tolgaozuygur/nightvision/pictures/20230412_170507.jpg

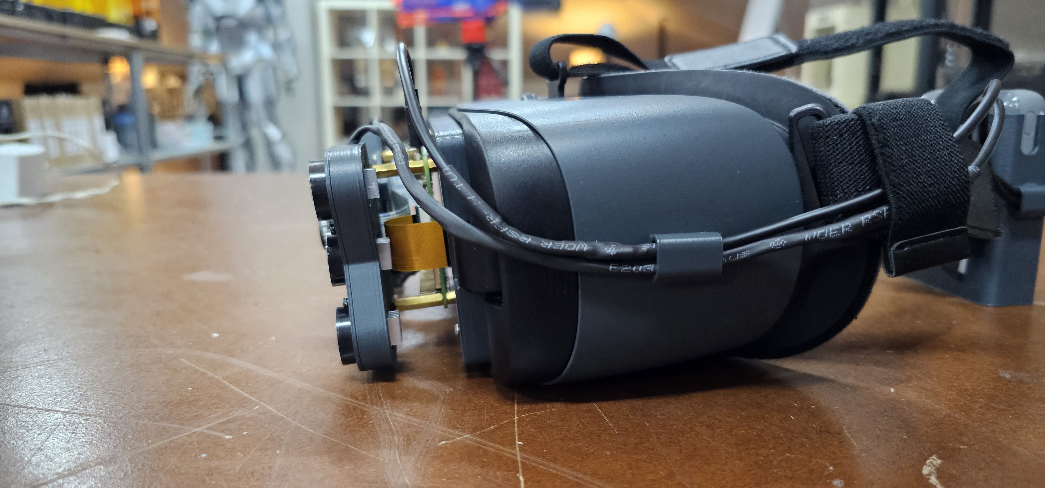
pictures/20230412_170507.jpg
