tolgaozuygur/nightvision/pictures/20230412_170524.jpg

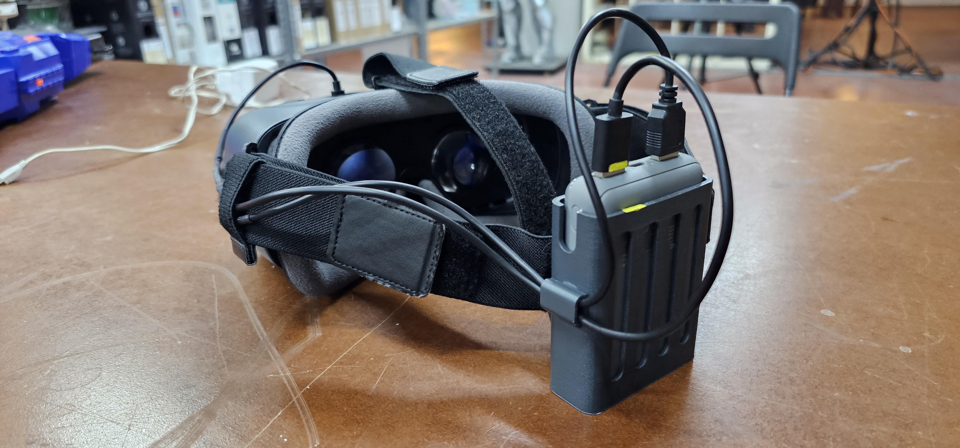
pictures/20230412_170524.jpg
